graham-r/kiCAD_RGB_ReversingCamera/RGB_ReversingCam_FSAV433_v3.1/images/RGB_ReversingCam_FSAV433_v3.1_SolderSide.png

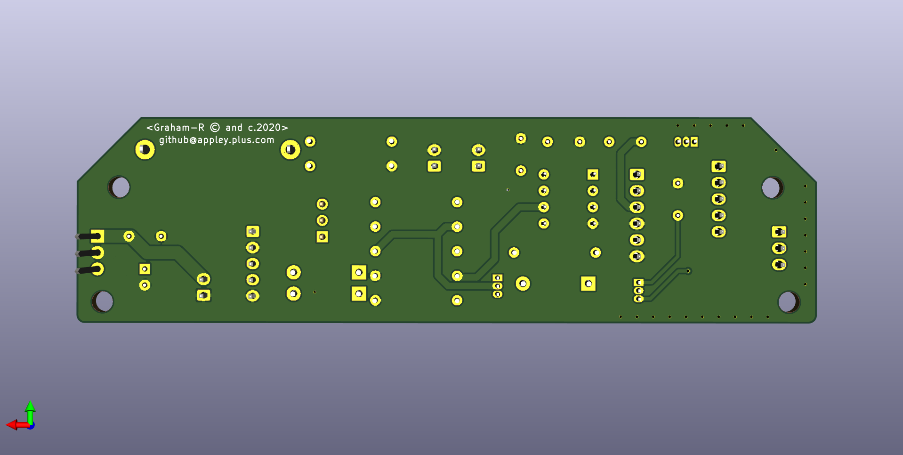
RGB_ReversingCam_FSAV433_v3.1/images/RGB_ReversingCam_FSAV433_v3.1_SolderSide.png
